BlackBrix/WinoBOARD_Breakout_passive/photos/IMG_20160225_171710270.jpg

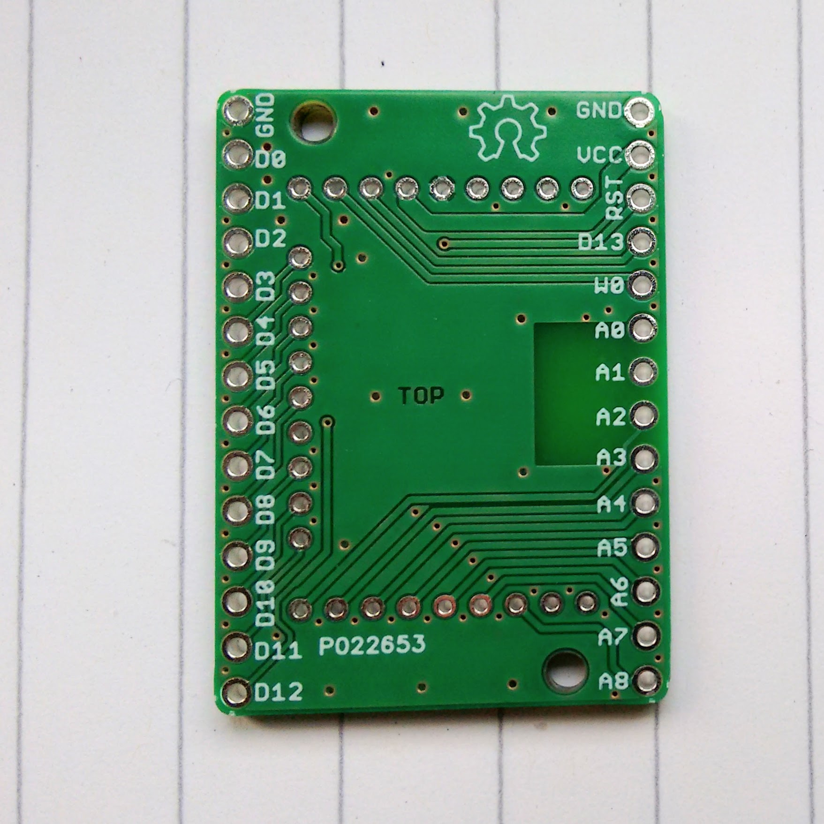
photos/IMG_20160225_171710270.jpg
