BlackBrix/WinoBOARD_Breakout_passive/photos/IMG_20160225_171757496.jpg

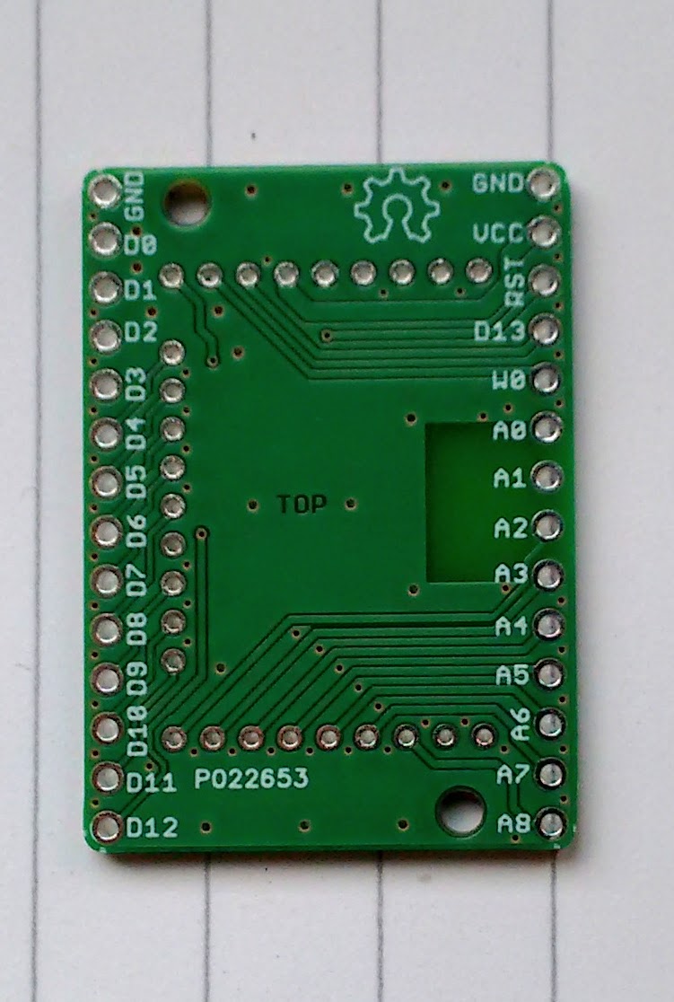
photos/IMG_20160225_171757496.jpg
