BlackBrix/WinoBOARD_Breakout_passive/photos/IMG_20160225_171813355.jpg

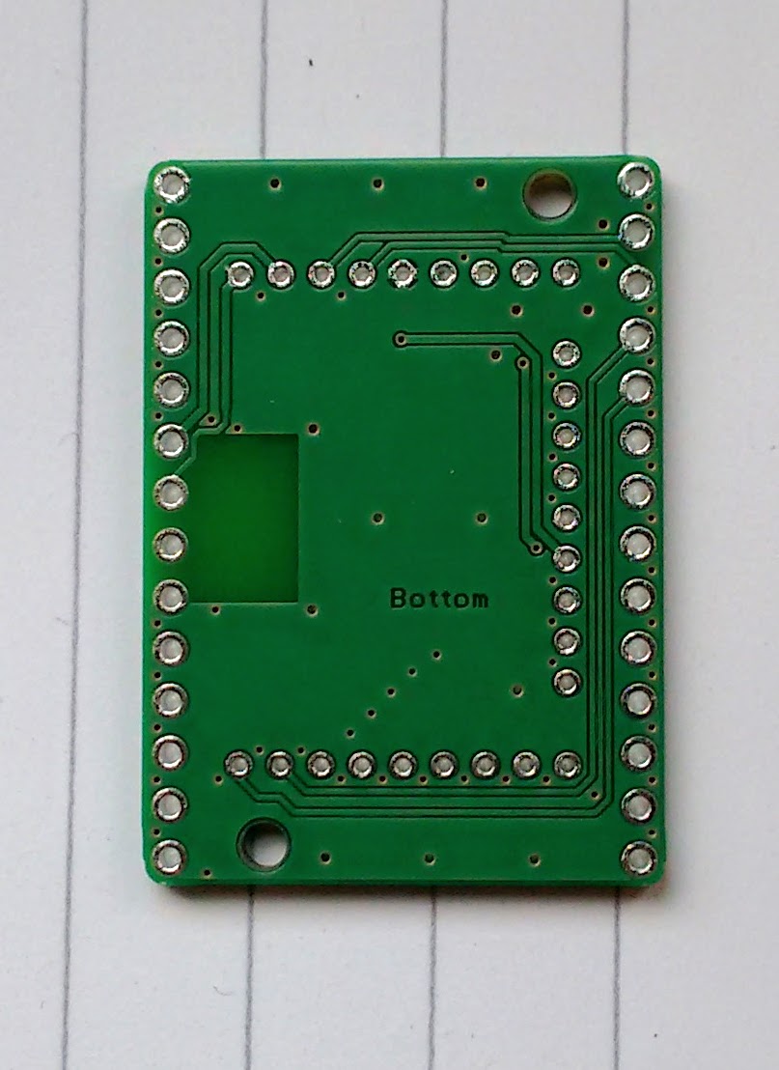
photos/IMG_20160225_171813355.jpg
