BlackBrix/WinoBOARD_Breakout_passive/photos/IMG_20160225_171933807.jpg

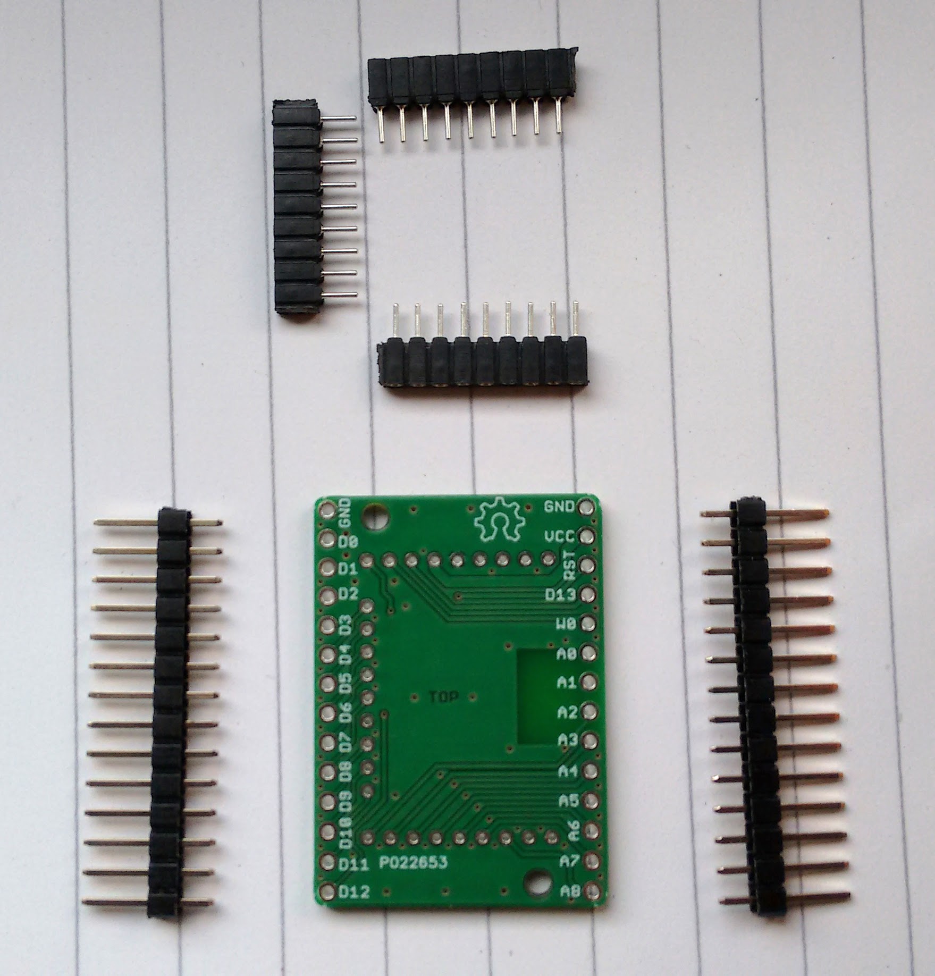
photos/IMG_20160225_171933807.jpg
