BlackBrix/WinoBOARD_Breakout_passive/photos/IMG_20160225_172111642.jpg

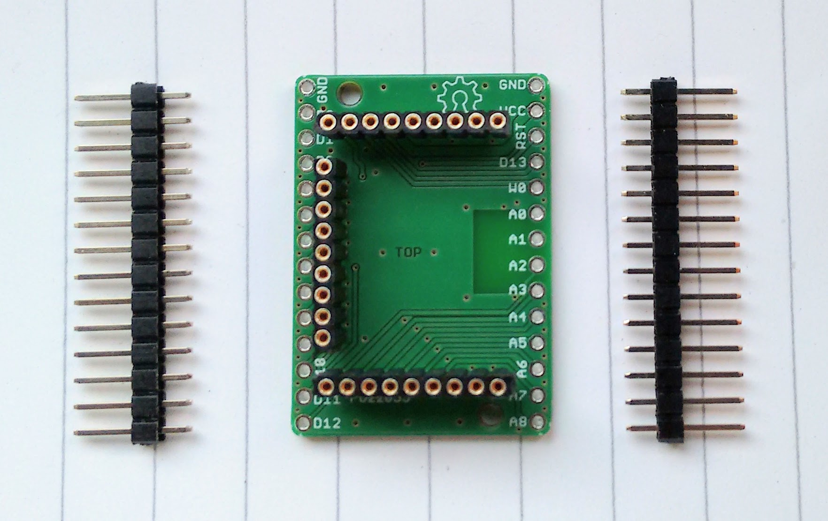
photos/IMG_20160225_172111642.jpg
