BlackBrix/WinoBOARD_Breakout_passive/photos/IMG_20160225_172452030.jpg

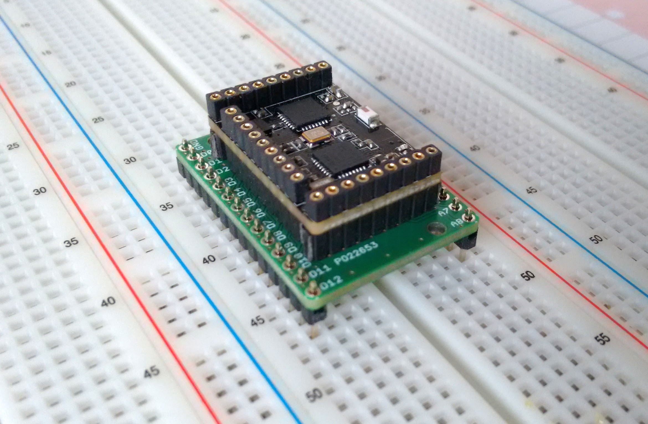
photos/IMG_20160225_172452030.jpg
