BlackBrix/WinoBOARD_Breakout_passive/photos/IMG_20160225_172535364.jpg

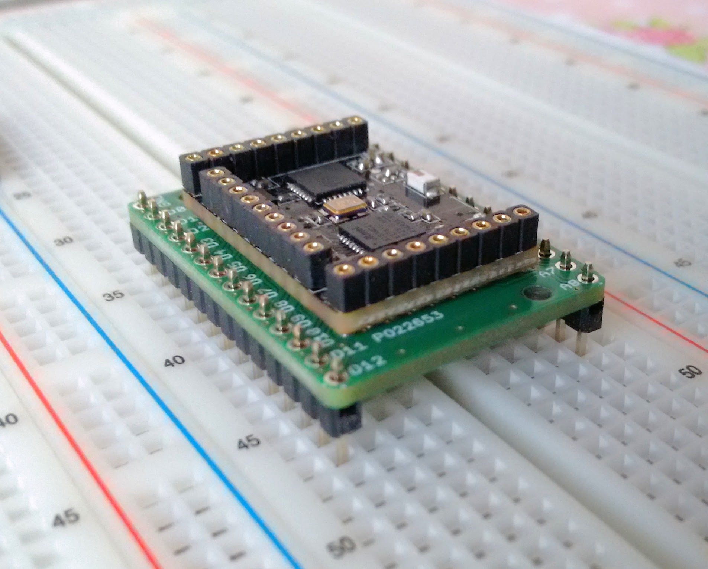
photos/IMG_20160225_172535364.jpg
