BlackBrix/WinoBOARD_Breakout_passive/photos/IMG_20160225_172607571.jpg

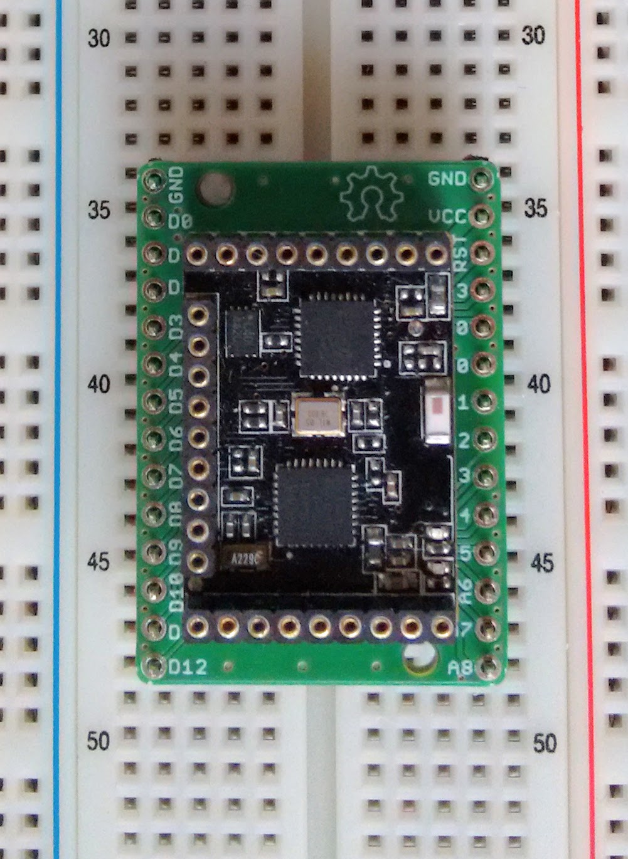
photos/IMG_20160225_172607571.jpg
